whowechina/mai_pico/cad/maimai_touch v2.png

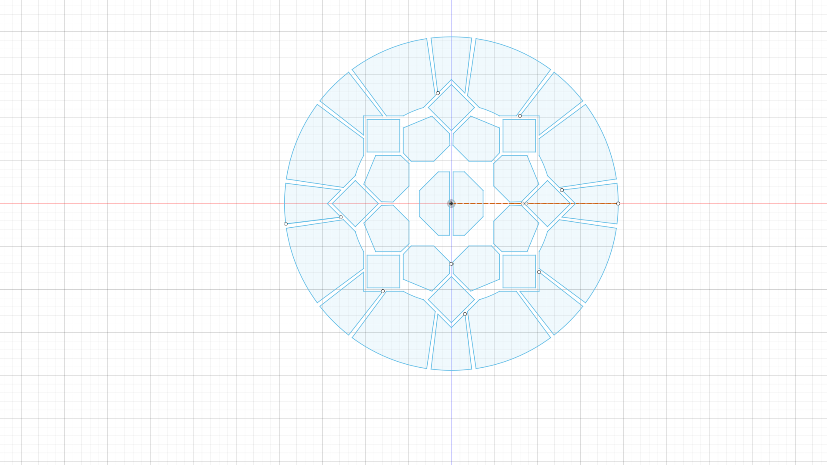
cad/maimai_touch v2.png
