whowechina/mai_pico/cad/maimai_touch v13.png

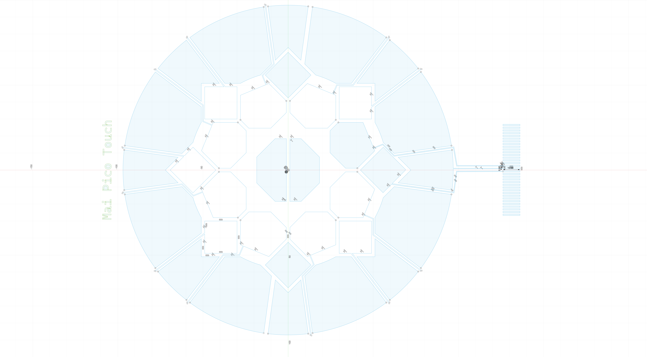
cad/maimai_touch v13.png
