whowechina/mai_pico/PCB/Button/3dmodels/J 2835.step

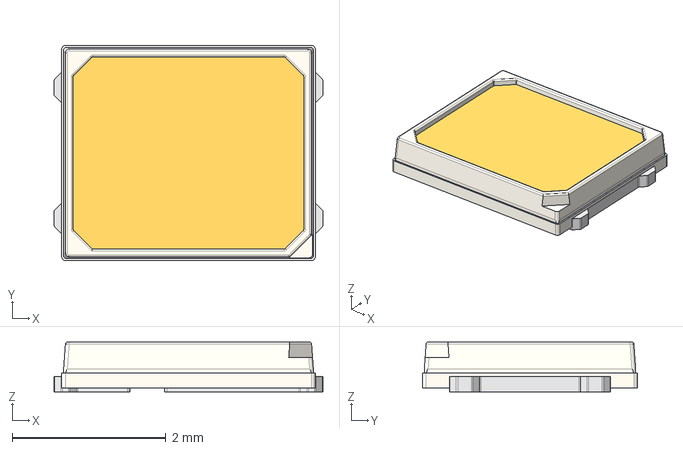
[picture p42: CAD file, 2023-08-30]
PCB/Button/3dmodels/J 2835.step
3.50 x 2.80 x 0.65 mm
