whowechina/mai_pico/PCB/IO/3dmodels/User Library-pj-393-8.STEP

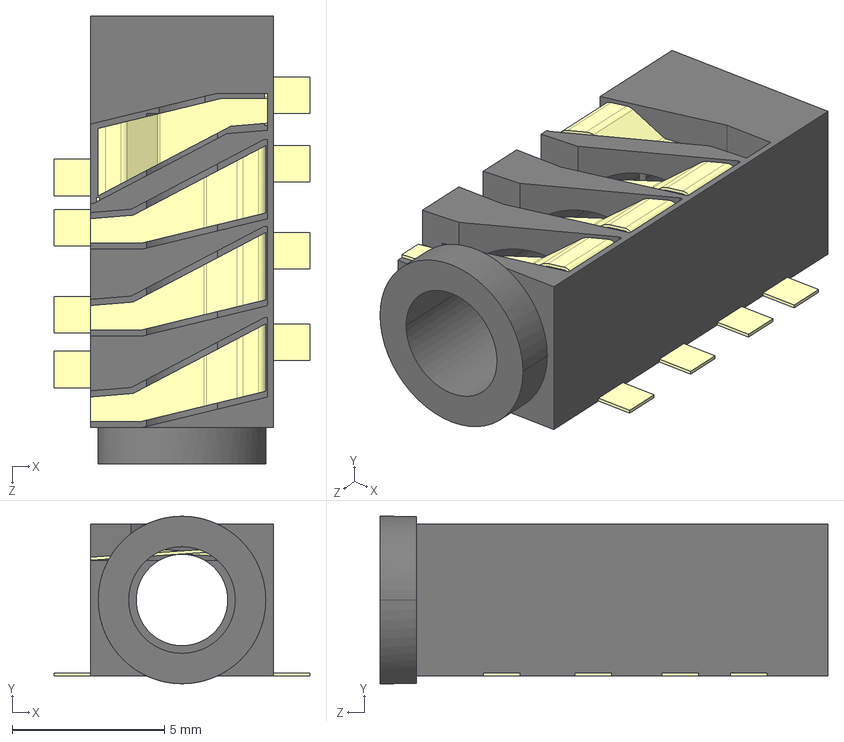
[picture p43: CAD file, 2023-08-30]
PCB/IO/3dmodels/User Library-pj-393-8.STEP
8.40 x 5.50 x 14.7 mm
PJ-393-8_1
PJ-393-8_2 x 4
PJ-393-8_3
PJ-393-8_4 x 3
