whowechina/mai_pico/PCB/IO/3dmodels/SW_Hotswap_Kailh_MX.stp

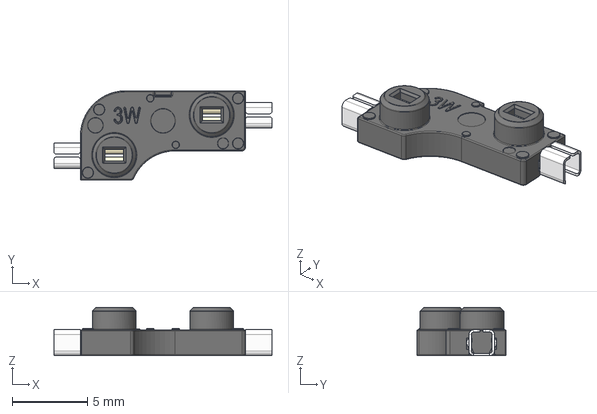
[picture p44: CAD file, 2023-08-30]
PCB/IO/3dmodels/SW_Hotswap_Kailh_MX.stp
14.5 x 5.95 x 3.22 mm
