whowechina/mai_pico/PCB/Button/3dmodels/Magnetic Pogo Connector 5 Pin (M) - 副本.STEP

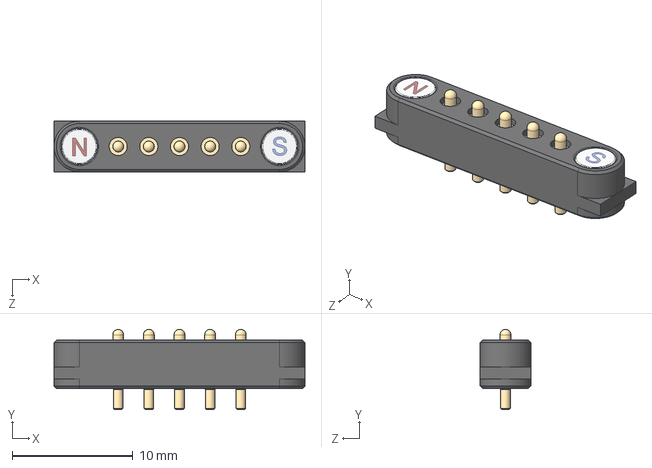
[picture p45: CAD file, 2023-08-30]
PCB/Button/3dmodels/Magnetic Pogo Connector 5 Pin (M) - 副本.STEP
20.8 x 6.65 x 4.20 mm
