whowechina/mai_pico/PCB/IO/3dmodels/Magnetic Pogo Connector 5 Pin (Type 3).STEP

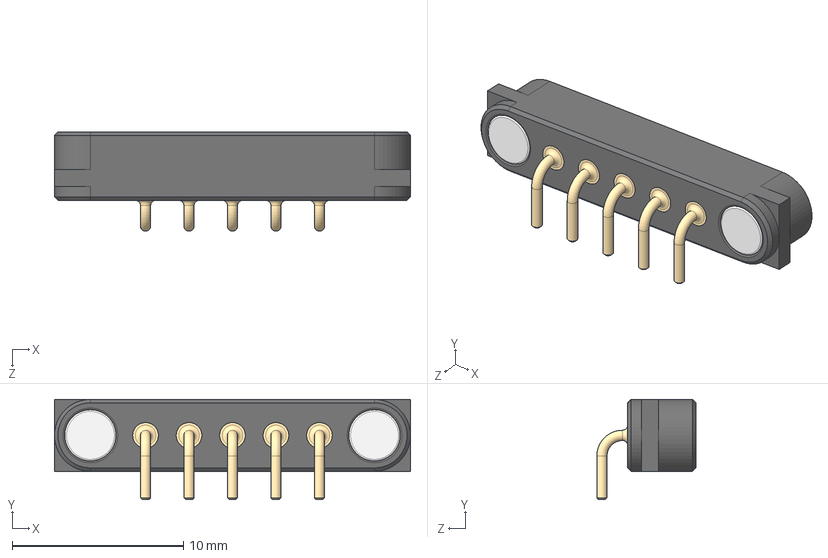
[picture p46: CAD file, 2023-08-30]
PCB/IO/3dmodels/Magnetic Pogo Connector 5 Pin (Type 3).STEP
20.8 x 5.85 x 5.80 mm
