whowechina/mai_pico/PCB/Button/3dmodels/SMD WS2812B-3535.step

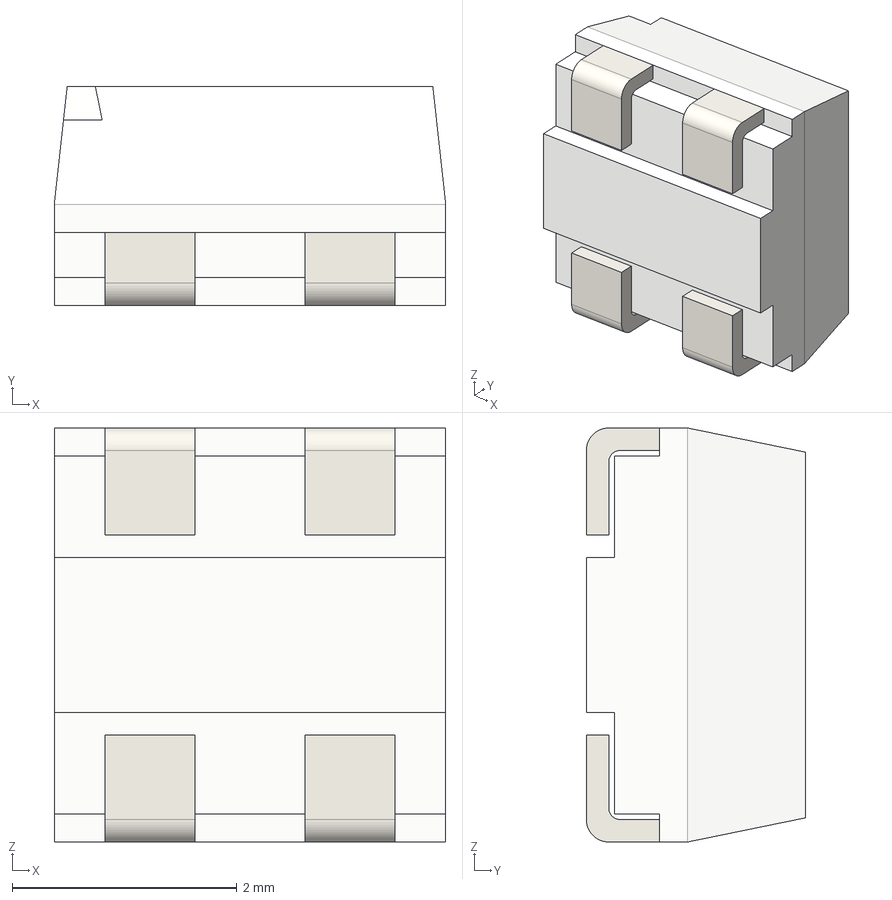
[picture p47: CAD file, 2023-08-30]
PCB/Button/3dmodels/SMD WS2812B-3535.step
3.48 x 1.95 x 3.68 mm
