whowechina/mai_pico/PCB/IO/3dmodels/User Library-WS2812-4020.step

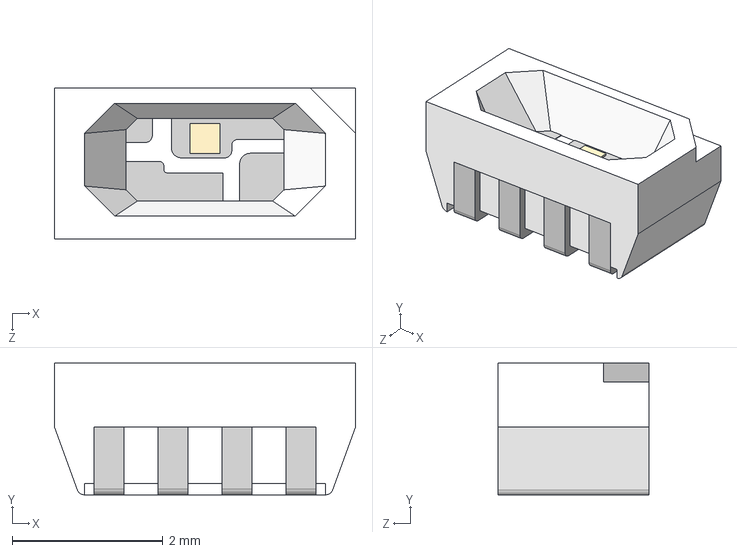
[picture p48: CAD file, 2023-08-30]
PCB/IO/3dmodels/User Library-WS2812-4020.step
4.00 x 1.75 x 2.00 mm
