whowechina/mai_pico/PCB/IO/3dmodels/Tact Switch 4.5mm SMT.step

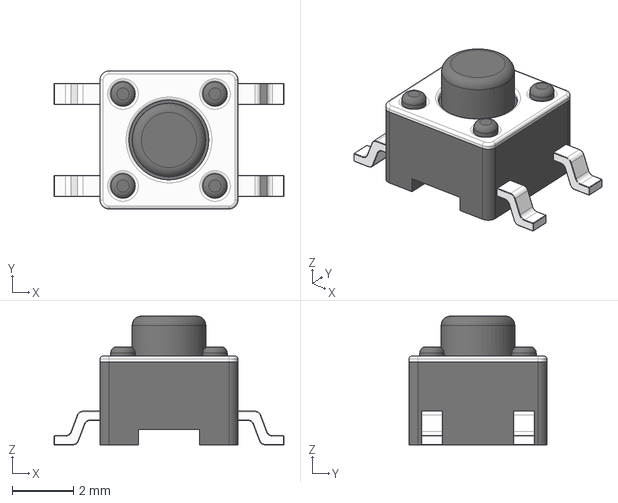
[picture p49: CAD file, 2023-08-30]
PCB/IO/3dmodels/Tact Switch 4.5mm SMT.step
7.50 x 4.50 x 4.20 mm
