whowechina/mai_pico/PCB/Button/3dmodels/Part Studio - pcb.step

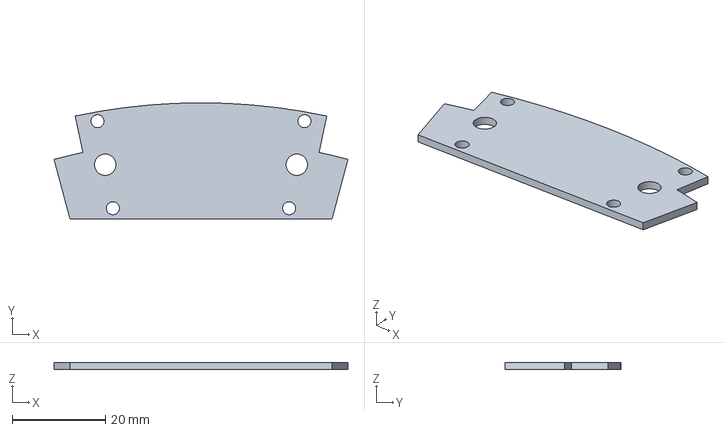
[picture p50: CAD file, 2023-08-30]
PCB/Button/3dmodels/Part Studio - pcb.step
63.2 x 25.0 x 1.60 mm
