whowechina/mai_pico/PCB/IO/3dmodels/Kailh LP Choc PC Keycap.step

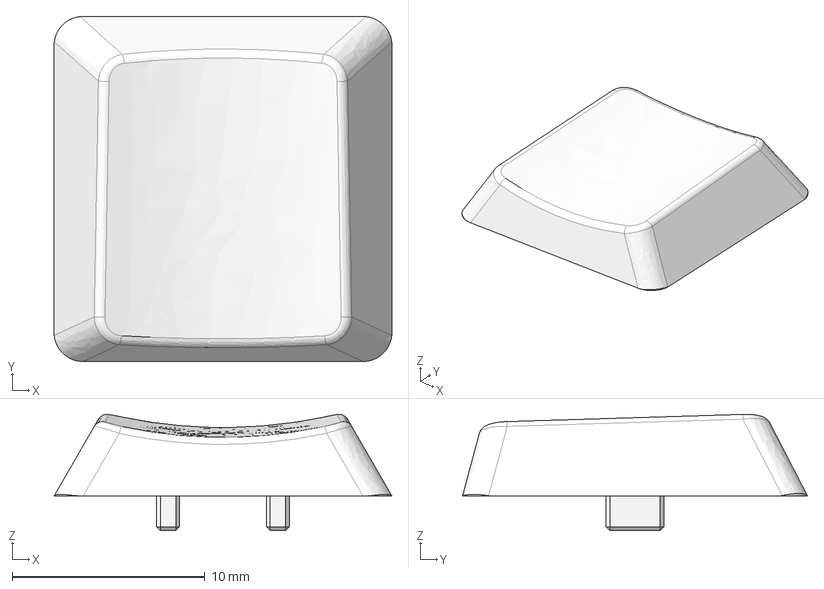
[picture p51: CAD file, 2023-08-30]
PCB/IO/3dmodels/Kailh LP Choc PC Keycap.step
17.5 x 17.9 x 6.03 mm
