whowechina/mai_pico/PCB/Button/3dmodels/User Library-WS2812-2020.step

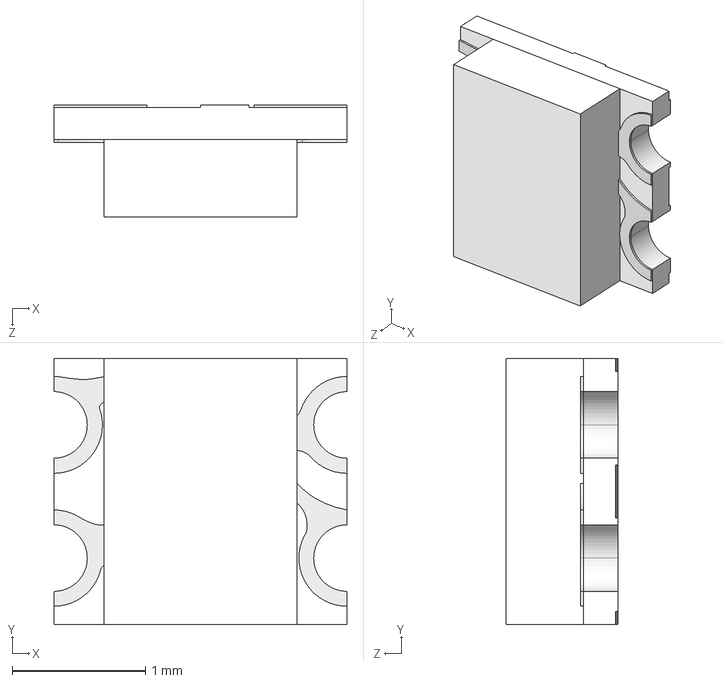
[picture p52: CAD file, 2023-08-30]
PCB/Button/3dmodels/User Library-WS2812-2020.step
2.20 x 2.00 x 0.84 mm
