whowechina/mai_pico/PCB/IO/3dmodels/WS2812B.step

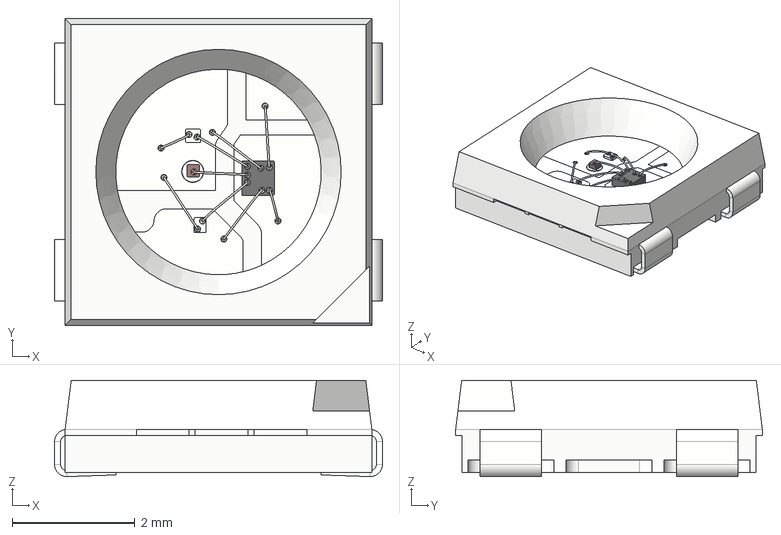
[picture p53: CAD file, 2023-08-30]
PCB/IO/3dmodels/WS2812B.step
5.35 x 5.00 x 1.57 mm
