whowechina/mai_pico/firmware/src/mpr121.h

/*
 * MPR121 Captive Touch Sensor
 * WHowe <github.com/whowechina>
 * 
 */

#ifndef MPR121_H
#define MPR121_H

#define MPR121_BASE_ADDR 0x5A

void mpr121_init(uint8_t addr);

uint16_t mpr121_touched(uint8_t addr);
bool mpr121_raw(uint8_t addr, uint16_t *raw, int num);
void mpr121_filter(uint8_t addr, uint8_t ffi, uint8_t sfi, uint8_t esi);
void mpr121_sense(uint8_t addr, int8_t sense, int8_t *sense_keys, int num);
void mpr121_debounce(uint8_t addr, uint8_t touch, uint8_t release);

#endif
