whowechina/mai_pico/firmware/src/button.h

/*
 * Mai Controller Buttons
 * WHowe <github.com/whowechina>
 */

#ifndef BUTTONS_H
#define BUTTONS_H

#include <stdint.h>
#include <stdbool.h>
#include "hardware/flash.h"

void button_init();

/* if anykey is pressed, no debounce */
bool button_is_stuck();

uint8_t button_num();
void button_update();
uint16_t button_read();
uint8_t button_real_gpio(int id);
uint8_t button_default_gpio(int id);

#endif
